whatnick/ADE7816_Breakout/doc/DRC_violations.PNG

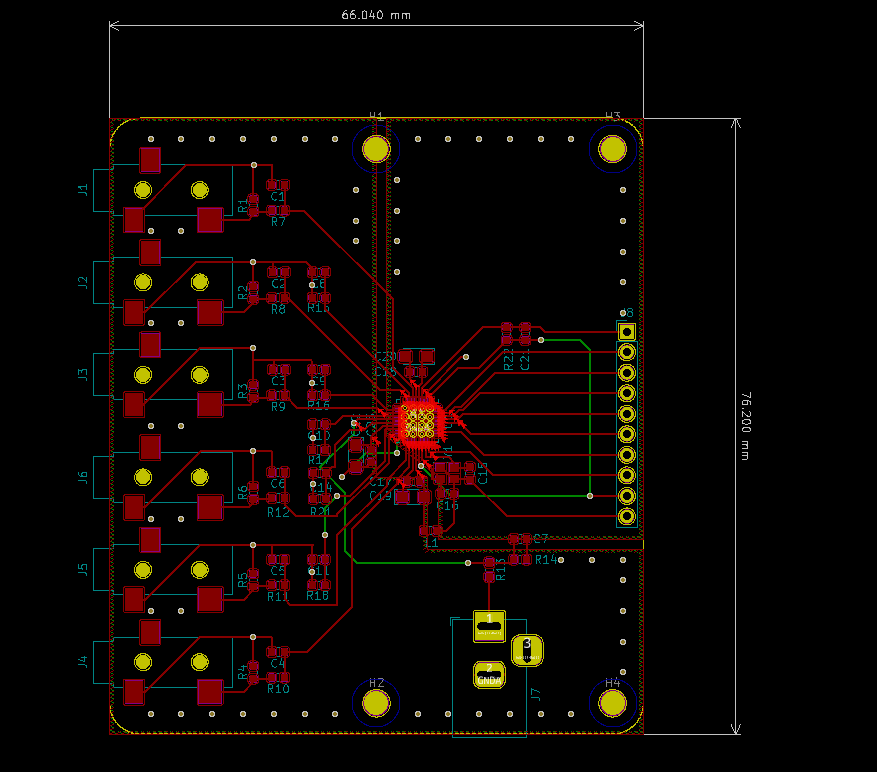
doc/DRC_violations.PNG
