whatnick/ADE7816_Breakout/doc/WIP_render.PNG

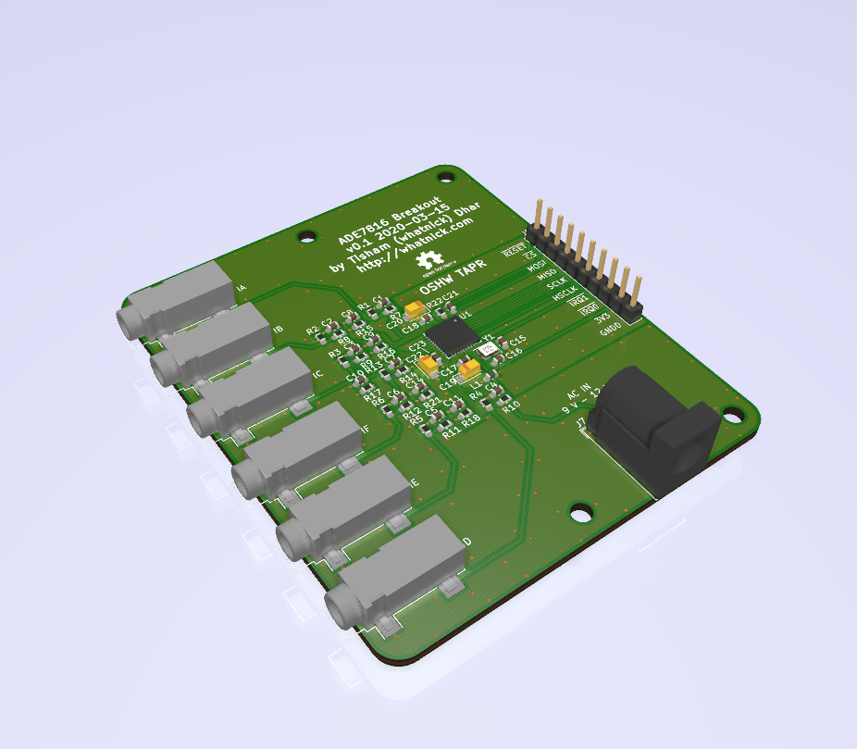
doc/WIP_render.PNG
